bcouraud/Linky-TIC-Reader/Publication/ISGT_2023/LaTEX/Battery_Scheduling_Lifespan.pptx

## Optimal Residential Battery Scheduling with Asset Lifespan Consideration

ISGT Europe 2020

B. Couraud, S. Norbu, M. Andoni, V. Robu, H. Gharavi, D. Flynn

## Context

- Paris Agreement: 32 kg → 5.5 kg CO2 eq/day
- Need to increase resident Renewable energy consumption

Reduction of Feed in Tariffs
→ Incentive for self consumption
Development of Residential batteries: Tesla, LG, …
How to optimally control batteries to reduce their simple payback period ?

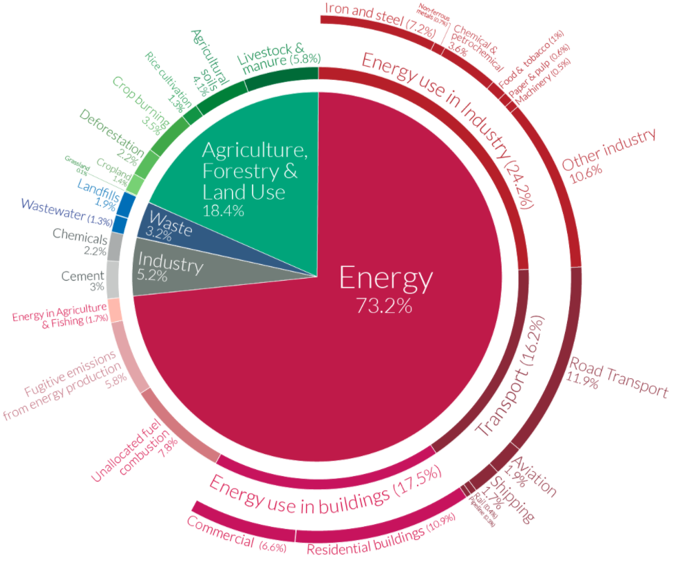
[picture p46: figure]

Source: https:// (https://ourworldindata.org/emissions-by-sector)ourworldindata.org/emissions-by-sector

## Battery Control Algorithms

Production forecast

Epv t

Demand forecast

Optimal scheduling forecast algorithm

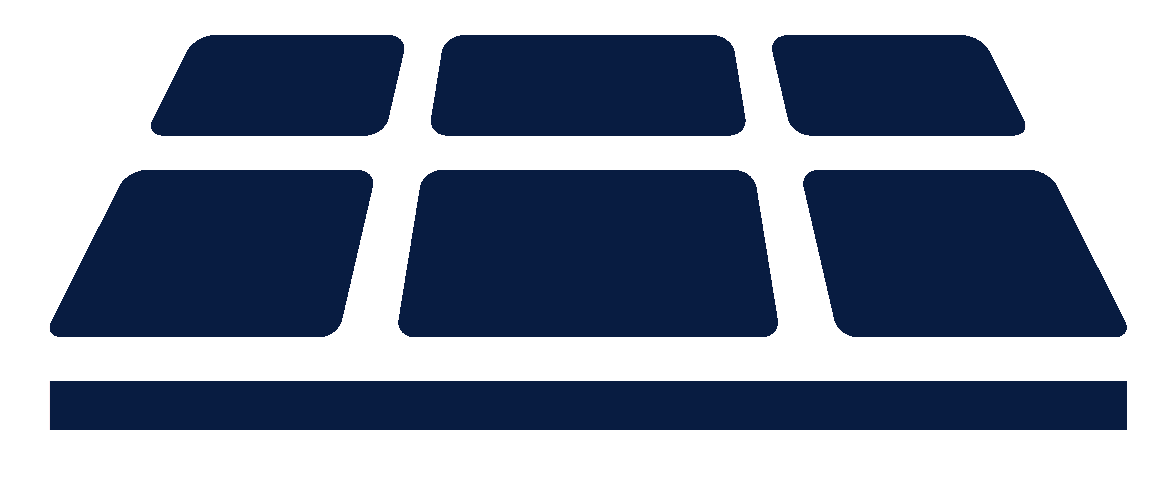
[picture p47: figure]

Ebat t

Prices forecast

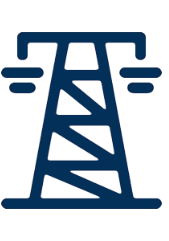
[picture p48: figure]
RÃ©sultat de recherche d'images pour "electric grid symbol"

Real Time production

Real Time demand

Battery control algorithm

Real Time price

Possible power flow

ED t

Optimization can be done using Linear Programming methods or evolutionary based algorithms
→ this work focuses on Linear Programming approaches

## Literature Review

- Battery control is a well studied field: charge/discharge schedule
- Cycles of battery operation affect its life time
- Optimization based schedules must include cycles into consideration
- Previous work only consider batteries with cycles starting from 100% State of Charge → need a new formulation

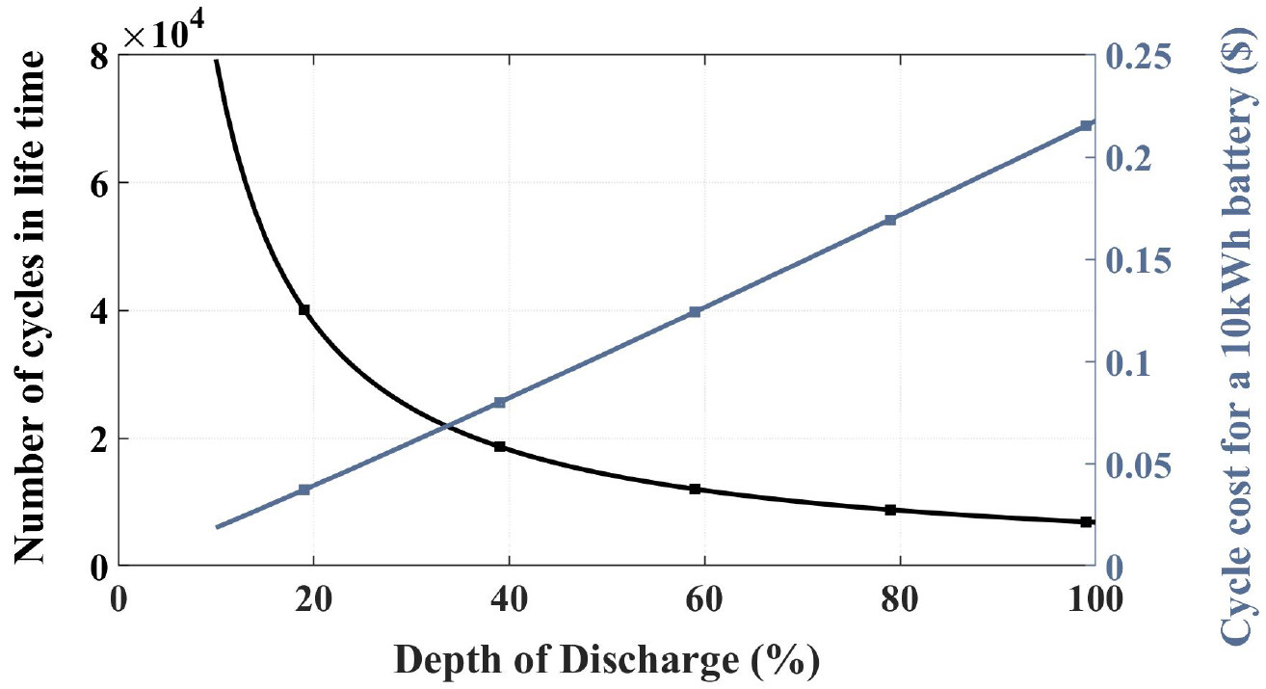
[picture p49: figure]

## Conventional Battery Control Optimization

- MILP Optimization problem:
minP_(bat)^t , t∈[0,24]E_i π_i −E_e π_e

Optimization variables:
Battery power for every time step (24 elements vector for e.g)
Other continuous/binary variables to ensure:
SoC limits are met
Household import and export are computed
Battery operation is physically possible (no simultaneous charge and discharge)

Battery Schedule

Energy import cost

Energy export revenue

## Optimisation Based Control

Example of implementation for day-ahead operations

100

SoC

0

Energy (kWh per 30 min)

Export Market price

Production Forecast

Demand Forecast

Export Forecast

Battery State of Charge

## Proposed Battery Control Optimization

- MILP Optimization problem:
minP_(bat)^t , t∈[0,24]E_i π_i −E_e π_e +CC

Additional variables:
Cycles depth
The Cycle depth variable is a 24 elements (e.g) vector where elements = 0 if the current cycle is not finished, and = cycle depth at the end of each cycle.
Other continuous/binary variables to compute the cycles depth.

Battery Schedule

Energy import cost

Energy export revenue

Cycles Cost

## Results

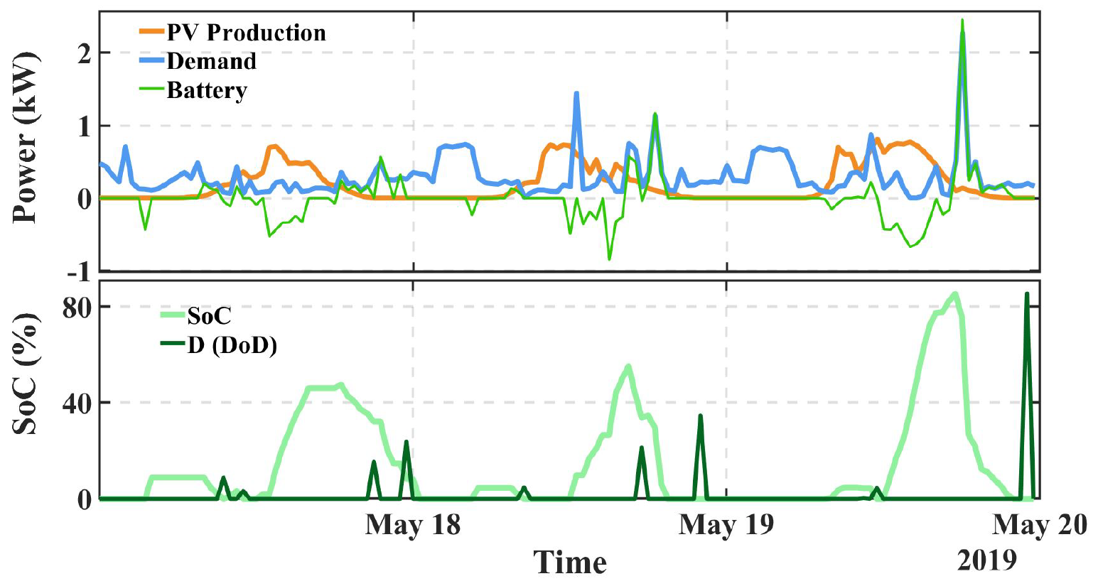
[picture p50: figure]

The implementation captures accurately charging and discharging cycles

## Discussion

Computing time compared to conventional approaches

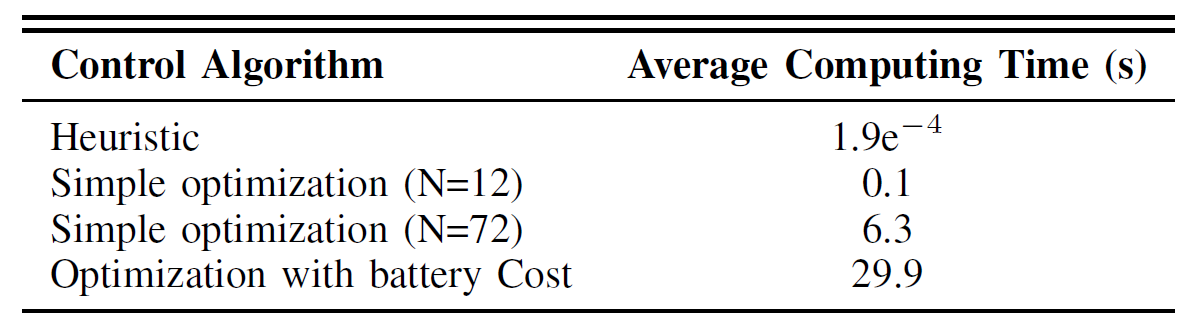
[picture p51: figure]

Comparison of expected electricity bills for different battery control algorithms:

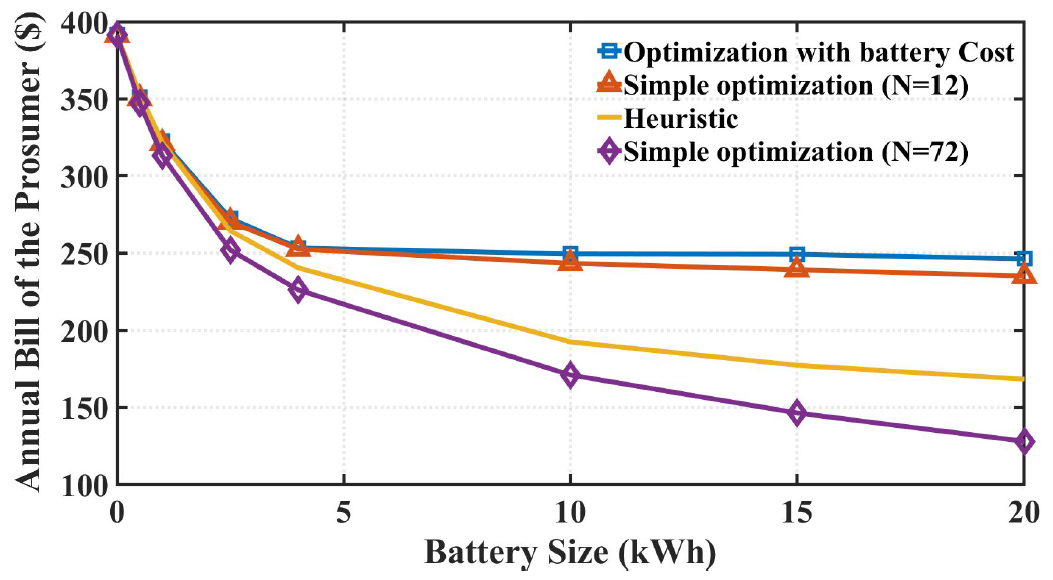
[picture p52: figure]
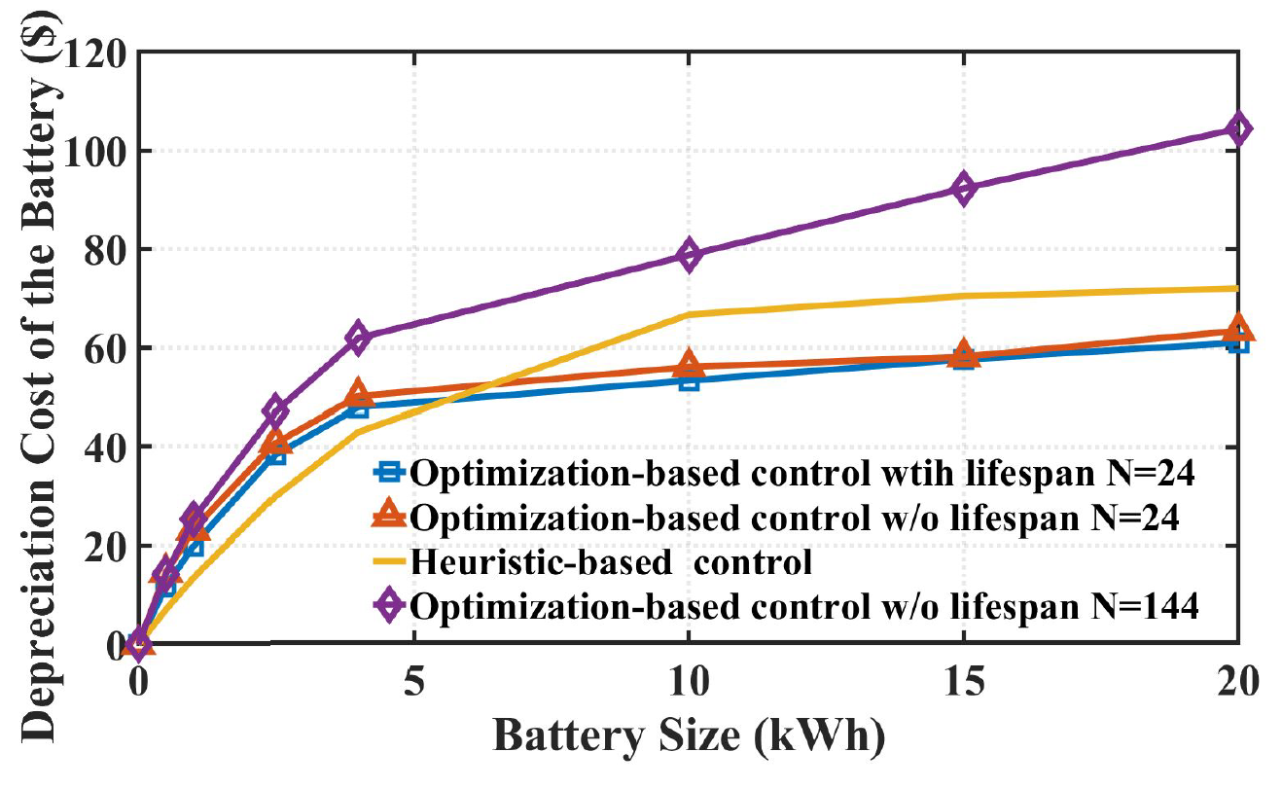
[picture p53: figure]

## Conclusion

- We proposed a new MILP optimization formulation for battery operation optimization that includes battery cycles impact
- Computation time is considerable
- For normal use, there is no tangible financial benefits compared to other existing methods

## Slide 11

Optimal Residential Battery Scheduling with Asset Lifespan Consideration

Optimal scheduling forecast algorithm

Production forecast

Epv t

Ebat t

Demand forecast

Prices forecast

Real Time production

Real Time demand

Battery control algorithm

Real Time price

Possible power flow

ED t

Optimization of Batteries’ schedule considering batteries cycling

MILP Optimization problem:
minP_(bat)^t , t∈[0,24]E_i π_i −E_e π_e +CC

However, it is computationally intensive, so requires a reduction of time horizon

Cycles Cost

Results

Battery Schedule

Energy import cost

Energy export revenue

Accurately capture Cycles Depth of Discharge
