bcouraud/Linky-TIC-Reader/Publication/ISGT_2023/LaTEX/Images/Imagesbis-DESKTOP-PKFPB98.pptx

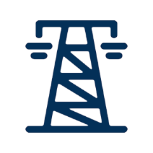
[picture p54: figure]
RÃ©sultat de recherche d'images pour "electric grid symbol"

Production forecast

Epv t

Demand forecast

Optimal scheduling forecast algorithm

Ebat t

RÃ©sultat de recherche d'images pour "electric grid symbol"

Real Time production

Prices forecast

Real Time demand

Battery control algorithm

Real Time price

Possible power flow

ED t

## Slide 2

Time step t

Is PPV(t) > Demand (t) ?

Yes

No

Is Battery full?

Is Battery empty?

Yes

No

Yes

No

Export PPV(t) -Demand (t) to grid

Charge with Pbat = min (Pbat max, PPV(t) -Demand (t))

Import PPV(t) -Demand (t) to grid

Discharge with Pbat = min (Pbat max, Demand (t) - PPV(t))

## Slide 3

## Slide 4

Forecasting Algorithms

Production forecast

Demand forecast

Prices forecast

Production forecast

Epv,t

Demand forecast

Prices forecast

Forecasting Algorithms

Battery Control Algorithms

Heuristic-based

Optimization-based w/o lifespan consideration

Optimization-based with lifespan consideration

Ebat,t

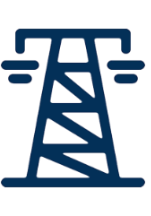
[picture p55: figure]
RÃ©sultat de recherche d'images pour "electric grid symbol"

Real Time production

Real Time demand

Real Time price

Possible power flow

ED,t

## Slide 5


LTR

## Slide 6

V1

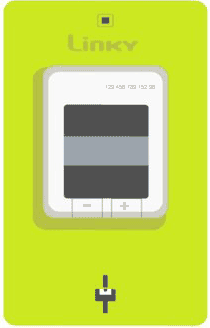
[picture p56: figure]

VS-10BQ015

1.5F
5.5V

9.1k

U1 :
PIC
12F1840

U1 :
PIC
12F1840

MCP
1825s33

270

C1

D1

Q1 : 2N7002

Power Supply

I2

I1

A

1k

BZT52H-B3V3

Double coils Latching Relay module

Actuator

3.3k

SFH6206

10k

U2:
LoRa or ESP
Node

Communication
& Control

Rx

A0

Set

BS170

Unset

12k - 22k

Demodulation

## Slide 7

4.5

3

Power (kW)

1.5

0

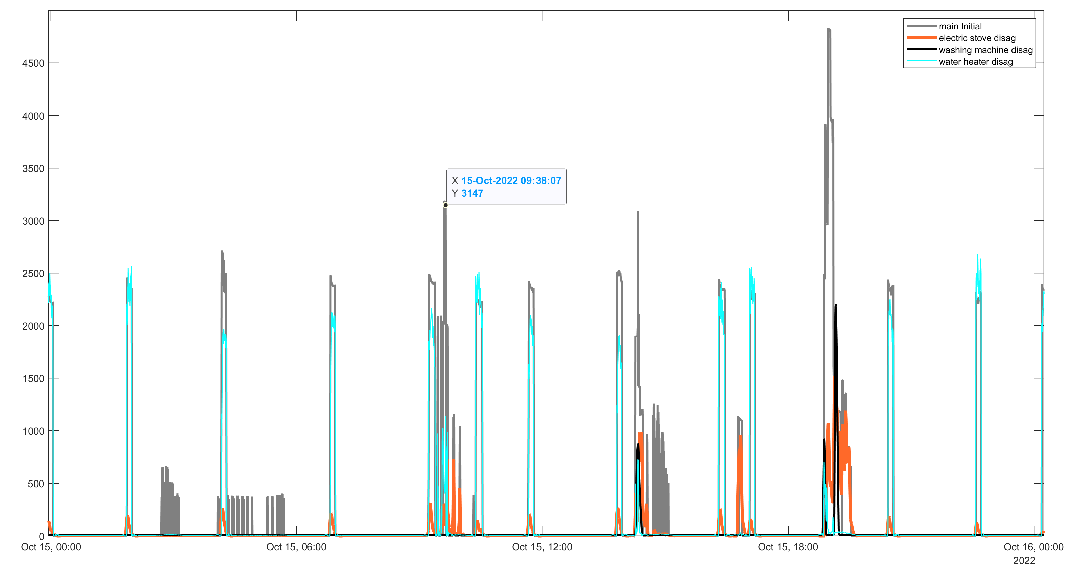
[picture p57: figure]

Water heater disaggregation

Main power (LTR data)

Electric Stove disaggregation

Oct. 16 00:00

Oct. 15 00:00

Oct. 15 06:00

Oct. 15 12:00

Oct. 15 18:00

## Slide 8

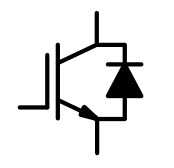
[picture p58: figure]
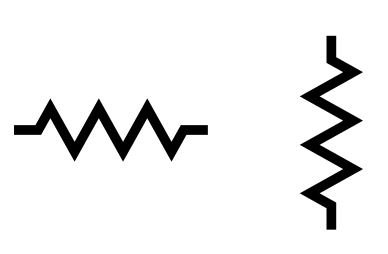
[picture p59: figure]
Image result for resistor symbol
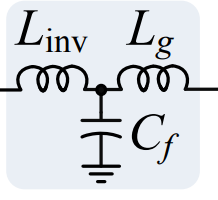
[picture p60: figure]

## Slide 9

PV Panels

Optional DC Converter

Inverter

PWMinv

abc

dq

Control Loop in dq frame

Filter + Coupling

Grid

Xf

r

1-3

VPV

iPV

VL

Vg

PWMinv

4-6

V_(g_(abc))

dq

abc

VPV

PWMpv

i_(g_(abc))

PLL

α

MPPT

mPWM abc

dq

abc

id iq

mPWM dq

Vgd Vgq

Reference Current Generator

Qtarget

Id target iq target

Ptarget

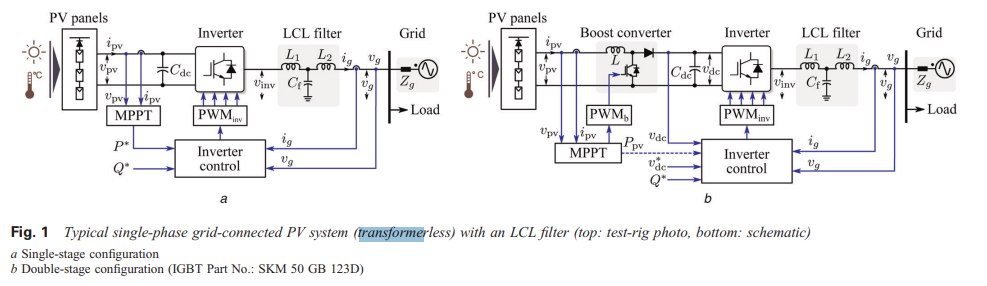
[picture p61: figure]

## Slide 10

V_g

jX_f i_g

i_g

V_L

r i_g

PV Panels

DC Converter

Single Phase Inverter

PWMinv

Filter + Coupling
(+ Transformer)

Grid

VPV

iPV

VL

Xf

r

Vg

VPV

PWMpv

VL

MPPT

Qref

Inverter & Reactive Power Control

Vg

ig

(a)

δ

φ

(b)
