bcouraud/Linky-TIC-Reader/Publication/ISGT_2023/LaTEX/ISGT2023-Residential_Flexibility.pdf

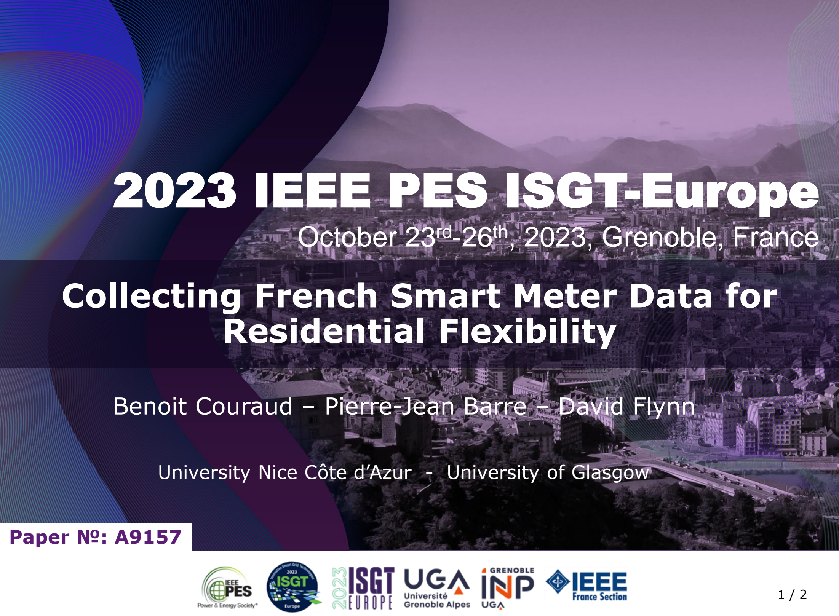
[picture p66: page 1]

# 2023 IEEE PES ISGT-Europe

# October 23rd-26th, 2023, Grenoble, France

# Collecting French Smart Meter Data for Residential Flexibility

## Benoit Couraud – Pierre-Jean Barre – David Flynn

## University Nice Côte d’Azur - University of Glasgow

## Paper №: A9157

1 / 2

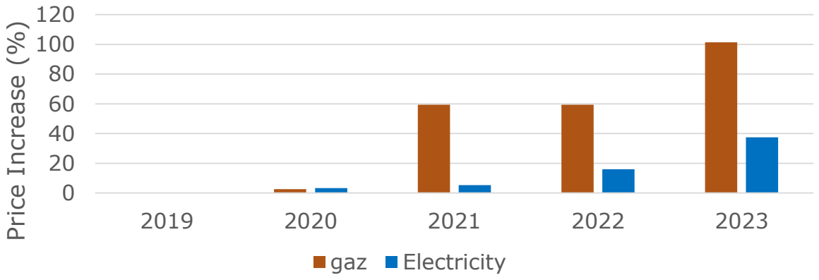
[picture p67: figure]
Price Increase (%); gaz; Electricity

2023 IEEE PES Innovative Smart Grid Technologies Conference Europe (ISGT-Europe), October 23rd-26th, 2023, Grenoble, France

# Introduction

# Energy Transition and gas-electricity prices evolution

# - residentials move from Gas heating to Electric - they request for a power rating increase

# Challenge: Distribution System Operators cannot easily increase Residentials power rating

# - Residential Flexibility could help deferring the grid reinforcement

2 / 2

# Similarly…

# How EV roll-out will affect local grid?

Low Voltage European Reference Network (~ 55 households)

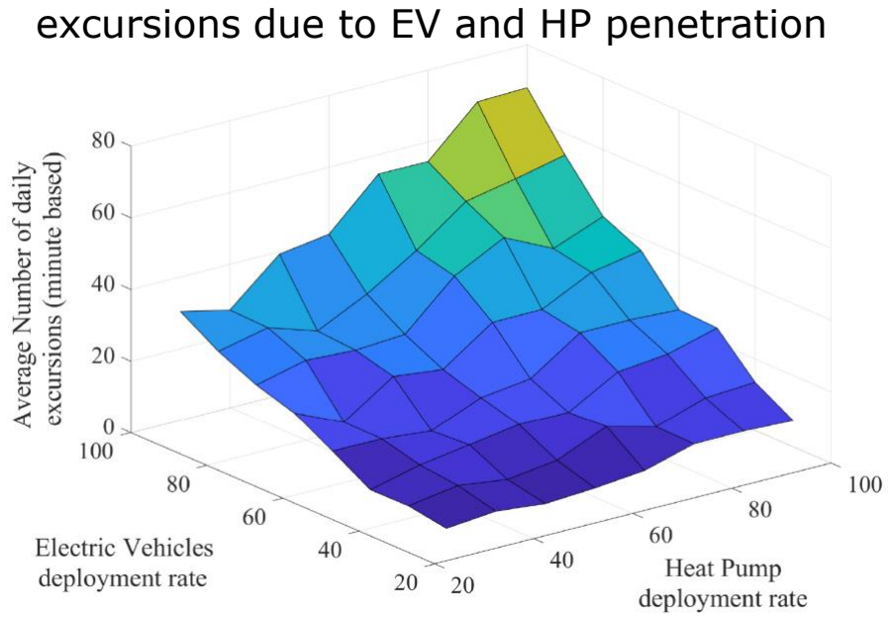
[picture p68: figure]
excursions due to EV and HP penetration
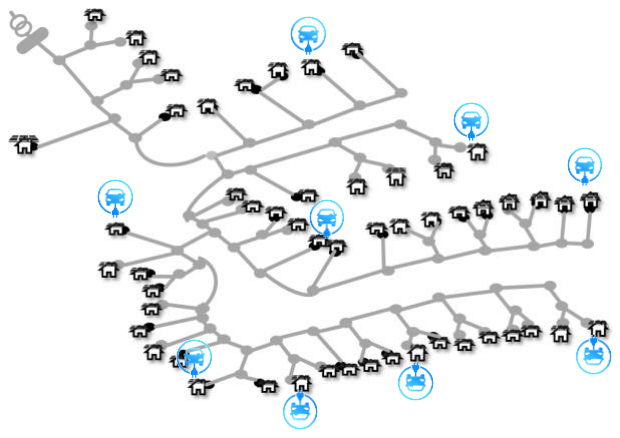
[picture p69: figure]

Monte-Carlo random allocation of EV roll-out using EV charging profiles from My Electric Avenue large scale experiment

Simulation results: Number of voltage

# - Residential Flexibility could help deferring the grid reinforcement

2 / 2

# Residential Flexibility

# Shifting of energy usage to prior / future times to reduce energy cost / avoid disconnection / …

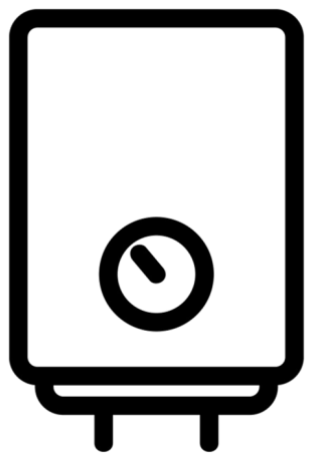
[picture p70: figure]

# Can be done through smart appliances – smart controller or … using a device connected to the Smart Meter ?

# - Leveraging the French Smart Meter to enable Residential Flexibility

# - We proposed a device that:

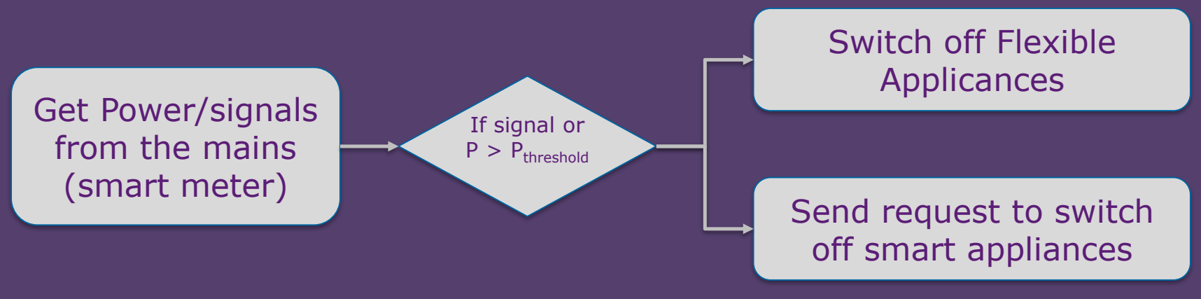
[picture p71: figure]
Get Power/signals from the mains (smart meter); Switch off Flexible Applicances; Send request to switch off smart appliances; If signal or; P > Pthreshold

2 / 2

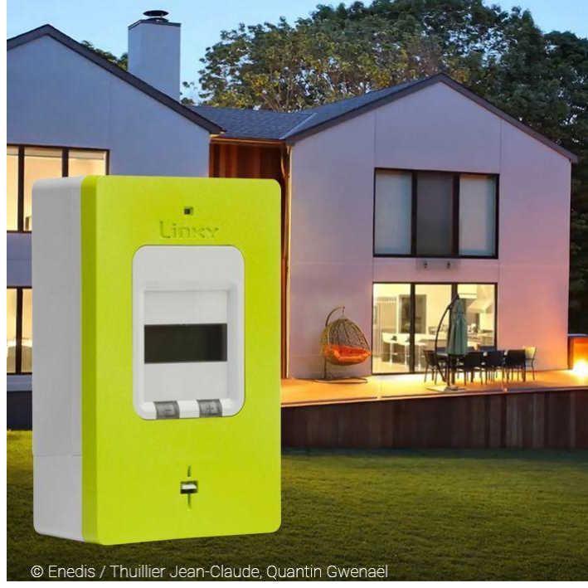
[picture p72: figure]

# French Smart Meter

# Disconnects household if overall power greater than rated power

# Collects load data and publish it every 30 min (next day publication) through PLC

# Local data available at a higher frequency (> 3s) through custom protocol (~modulated UART) + very small local supply (< 130mW)

# - Concept = monitor data in real time and disconnect specific loads (Evs, water heater) when overall power increases dangerously

# Connecting to the French Smart Meter

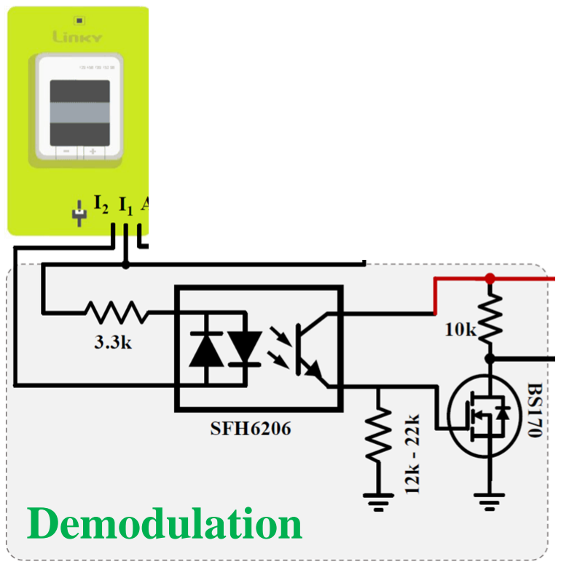
[picture p73: figure]
Demodulation

# Connecting to the French Smart Meter

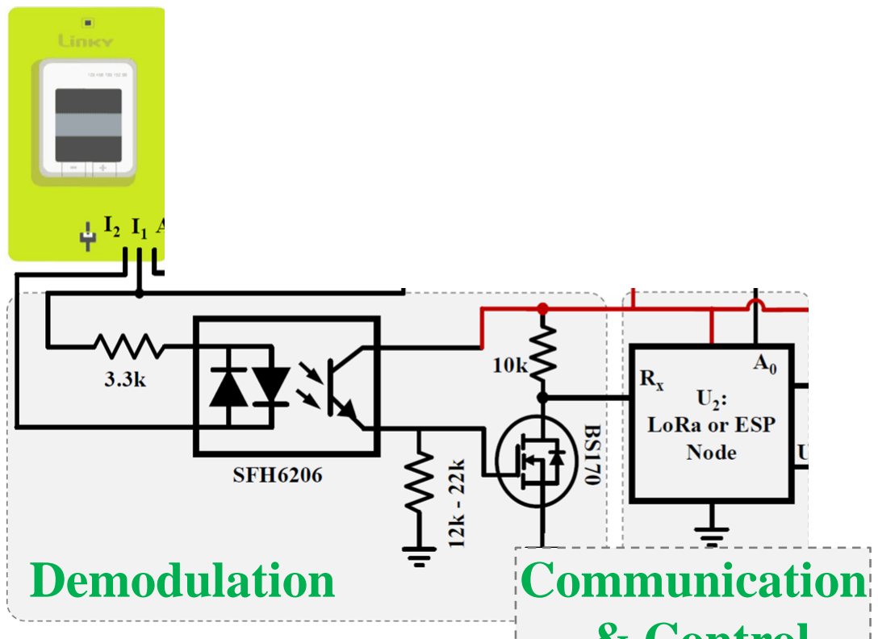
[picture p74: figure]
Demodulation; Communication

## & Control

# Connecting to the French Smart Meter

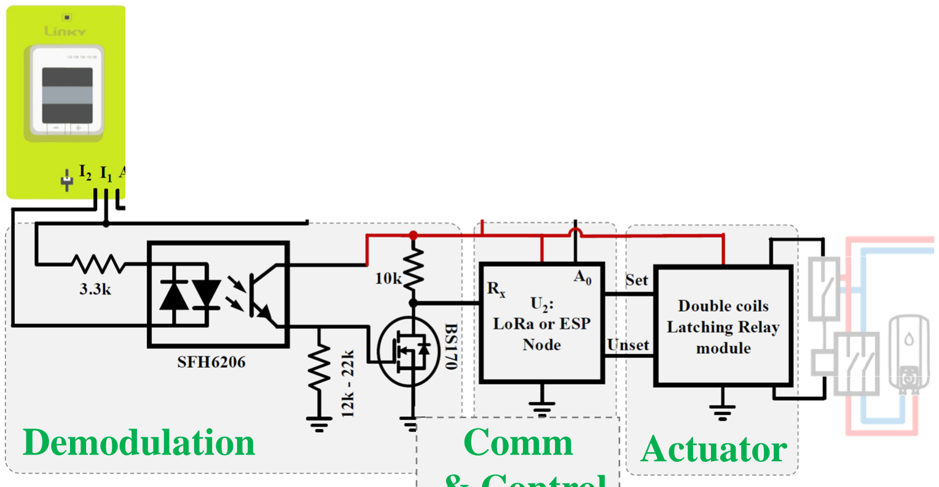
[picture p75: figure]
Demodulation; Comm; Actuator

## & Control

# Connecting to the French Smart Meter

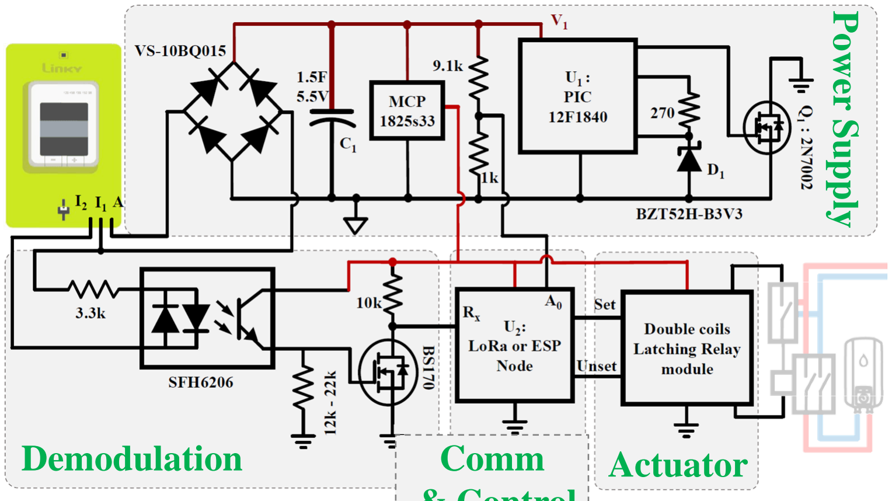
[picture p76: figure]
Demodulation; Comm; Actuator; Power Supply

## & Control

# Connecting to the French Smart Meter

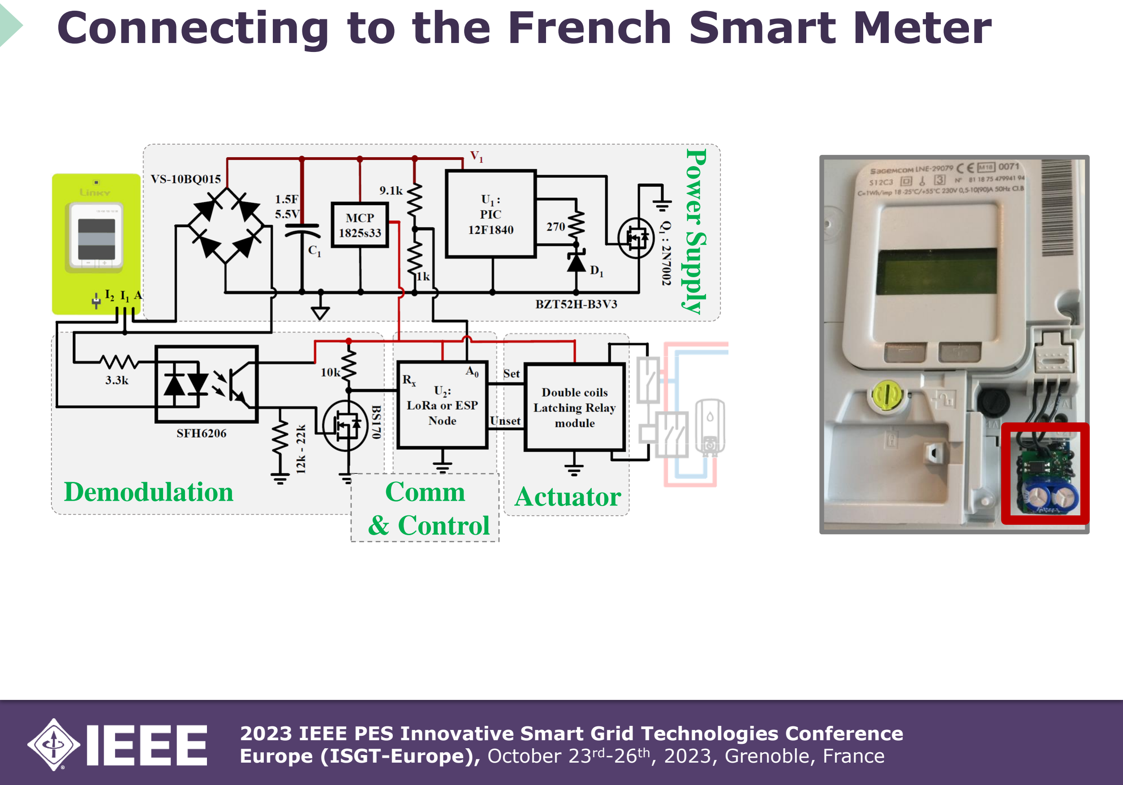
[picture p77: page 13]

Demodulation | Comm & Control

## Actuator

## Power Supply

# Challenge: Power Supply Strategy

# Very low power supply from the Smart Meter

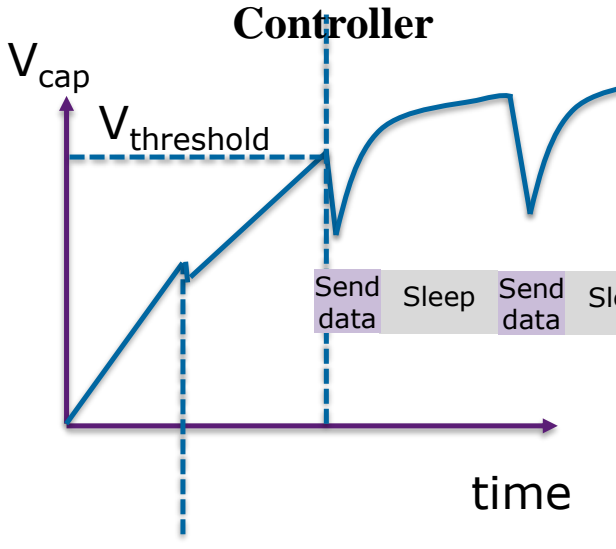
[picture p78: figure]
time; Vcap; Vthreshold; Controller; Sleep Send data; Send data; Sleep
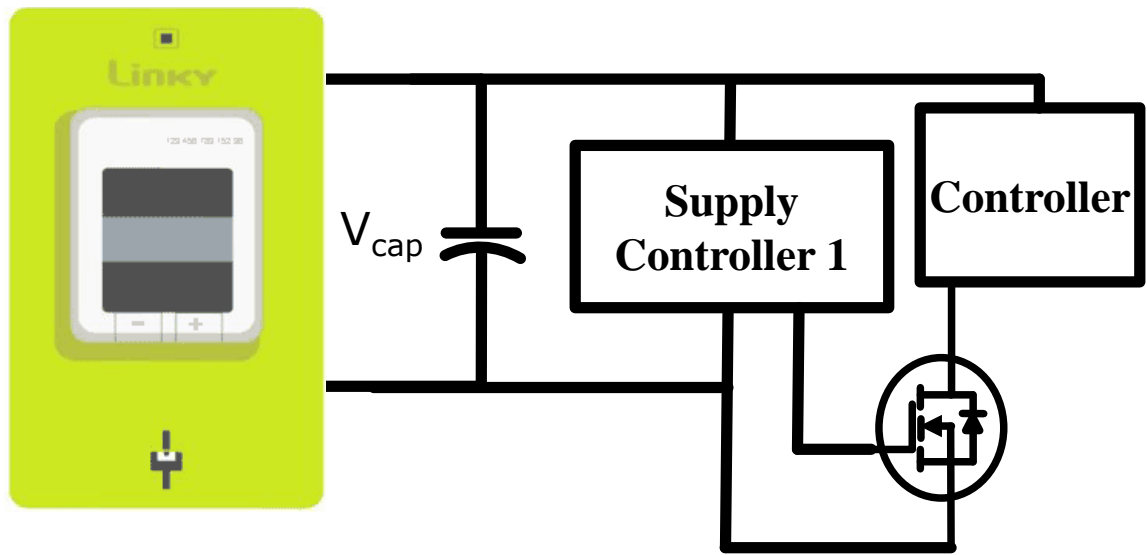
[picture p79: figure]
Vcap; Supply; Controller; Controller 1

## Supply Controller 1 switches on

## Switch on

# Experimental Results

2 / 2

# Experimentation

# Successfully installed in 6 Households with correct switching behaviour when overloading

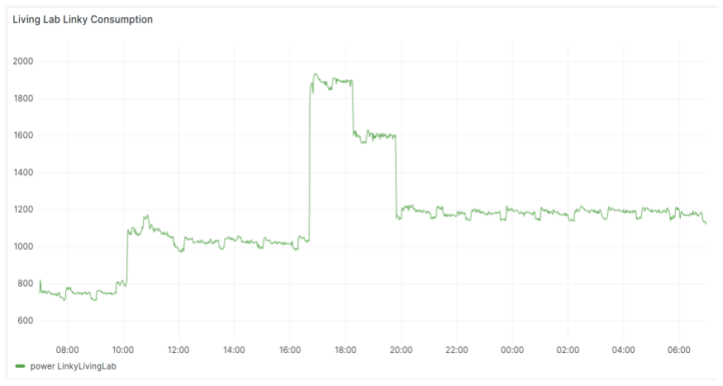
[picture p80: figure]
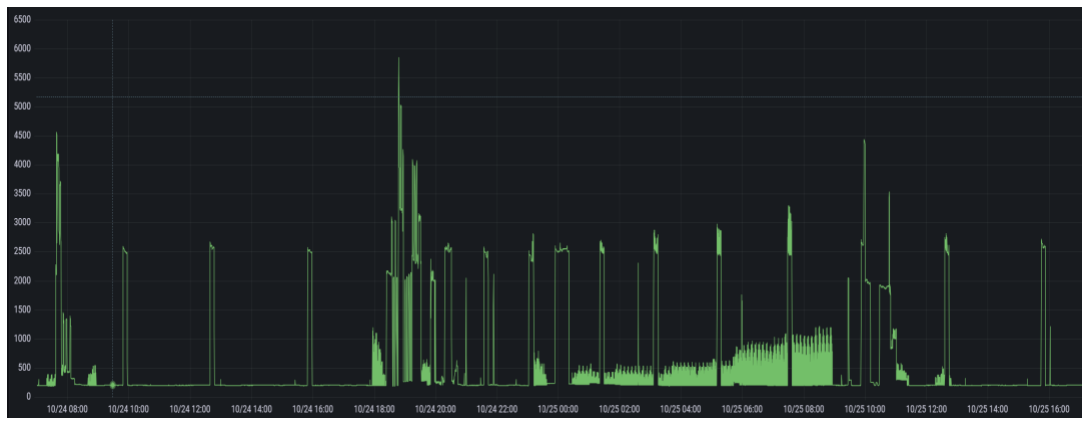
[picture p81: figure]

# Also used for other purposes…

# Leveraging Smart Meter Data

# Residential Non-Intrusive Load Monitoring from

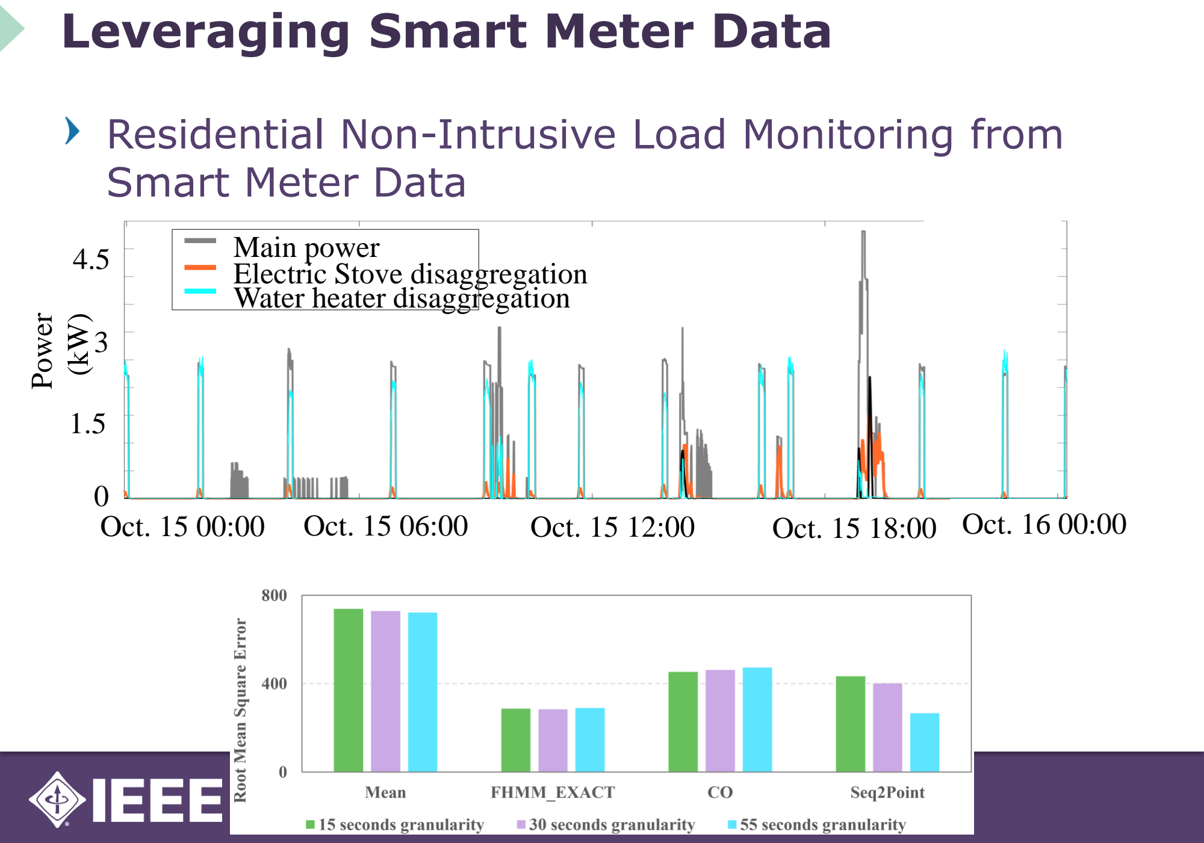
[picture p82: page 17]

# Smart Meter Data

## Main power Electric Stove disaggregation Water heater disaggregation

Oct. 15 00:00 | Oct. 15 06:00 | Oct. 15 12:00 | Oct. 15 18:00 | Oct. 16 00:00

4.5

3

1.5

0

## Power

(kW)

# Leveraging Smart Meter Data

# Residential Load Forecasting Assessment study

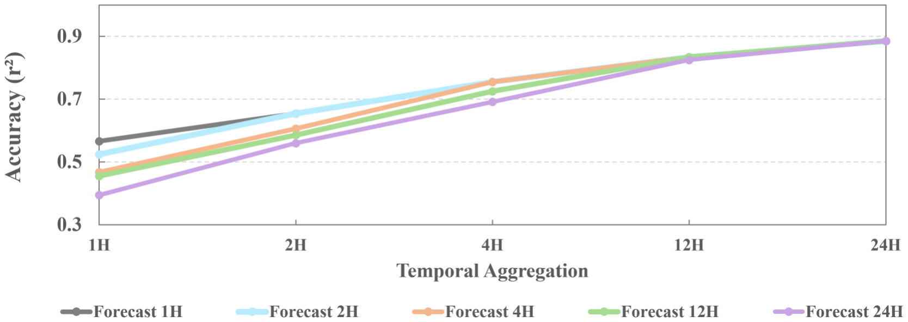
[picture p83: figure]

# Conclusions

# Successfully provided a small device to collect data and activate flexible appliances

→ open access: https://github.com/bcouraud/Linky-TIC-Reader

# Smart Meter data has potential for NILM → need more datasets

# Smart Meter Data for single house’s load prediction can be used but accuracy > 70% only if temporal aggregation > 4h

2 / 2

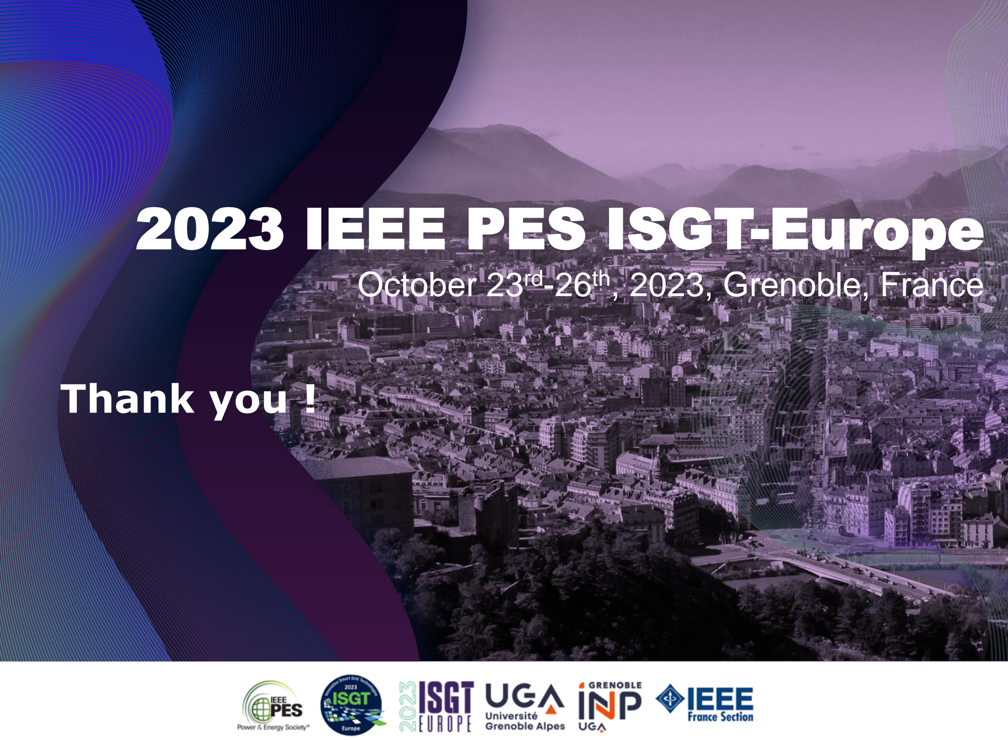
[picture p84: page 20]

# 2023 IEEE PES ISGT-Europe

# October 23rd-26th, 2023, Grenoble, France

# Thank you !
