bcouraud/Linky-TIC-Reader/Serveur_Get_Data_postgres_2022/Server_Data_Linky/javascript/ReadMe.txt

First, a cluster was created on Atlas.
https://cloud.mongodb.com/    https://cloud.mongodb.com/v2/62fdf34a3d83de17a33f3030#clusters 
benoit.couraud@glasgow.ac.uk
password = Topologie1

a collection "powerdata" was created.

for local mongodb
https://www.prisma.io/dataguide/mongodb/setting-up-a-local-mongodb-database

I created a folder for data: C:\mongoData\db

Then, had to run mongod.exe: dans le terminal (cmd) windows:
C:\Users\Benoit Couraud>cd C:\

C:\>cd MongoData

C:\MongoData>cd db
C:\MongoData\db>"C:\Program Files\MongoDB\Server\5.0\bin\mongod.exe"
